florianwns/keyboard-fatar-tp40/images/IMG_2003.jpg

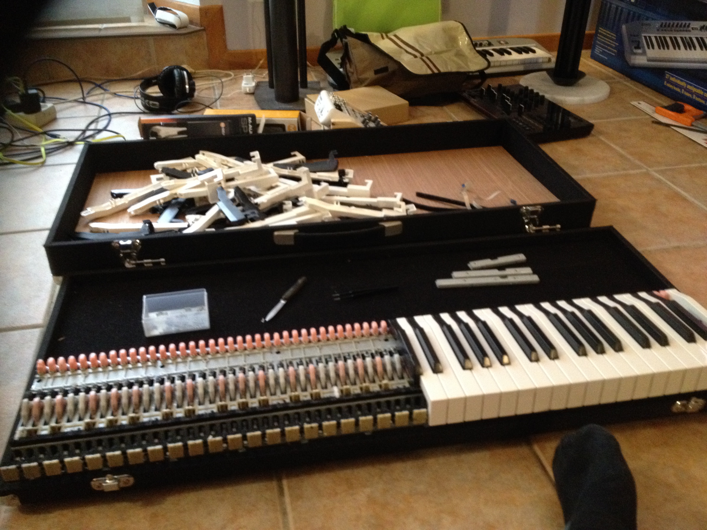
images/IMG_2003.jpg
