florianwns/keyboard-fatar-tp40/images/IMG_2004.jpg

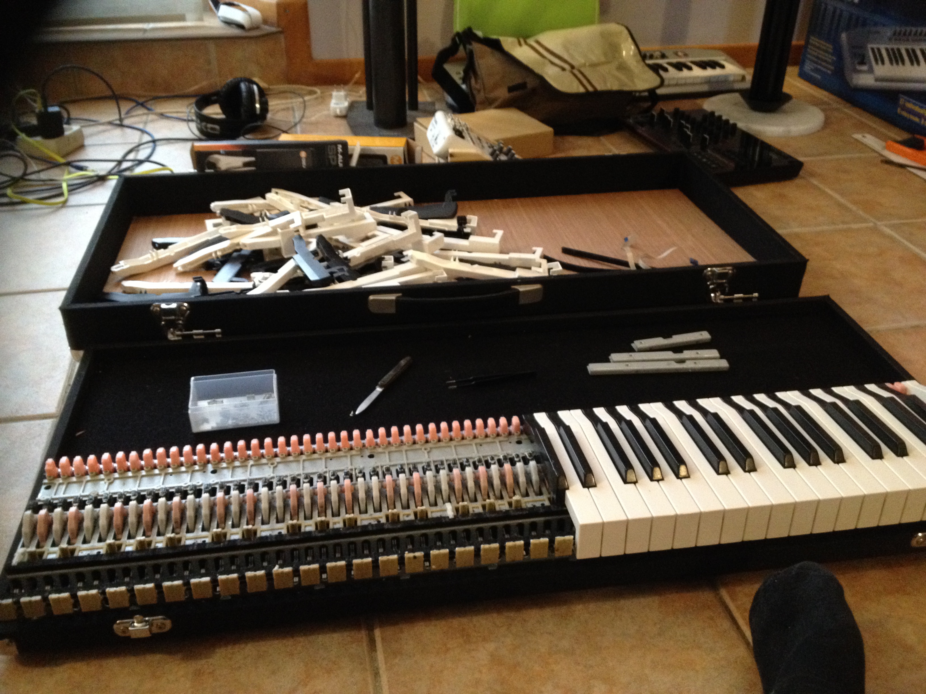
images/IMG_2004.jpg
