florianwns/keyboard-fatar-tp40/images/IMG_2005.jpg

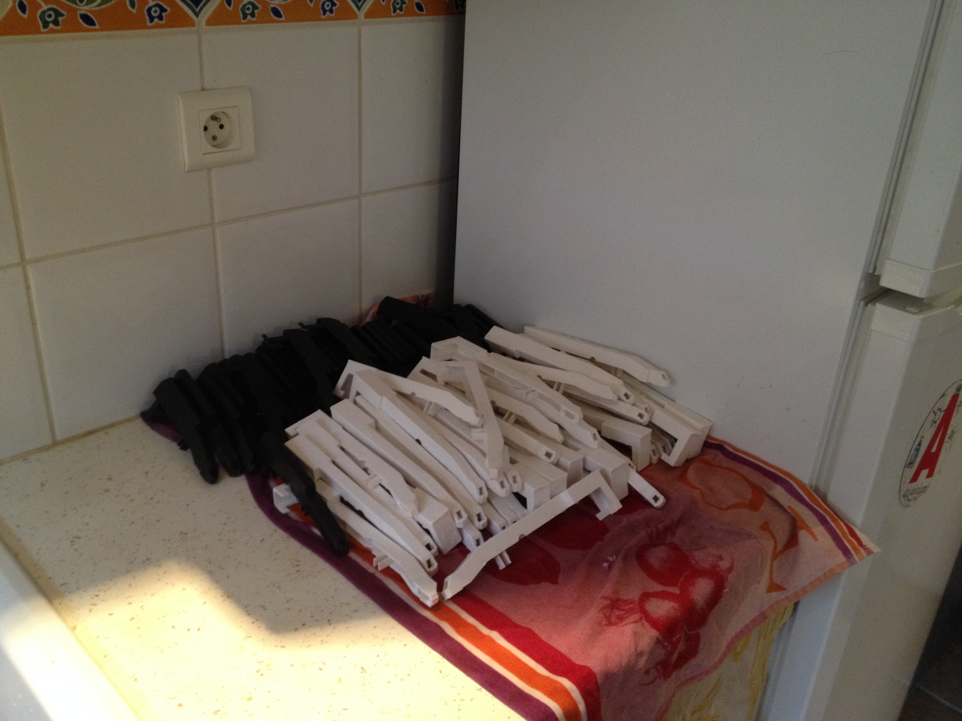
images/IMG_2005.jpg
