florianwns/keyboard-fatar-tp40/images/IMG_2006.jpg

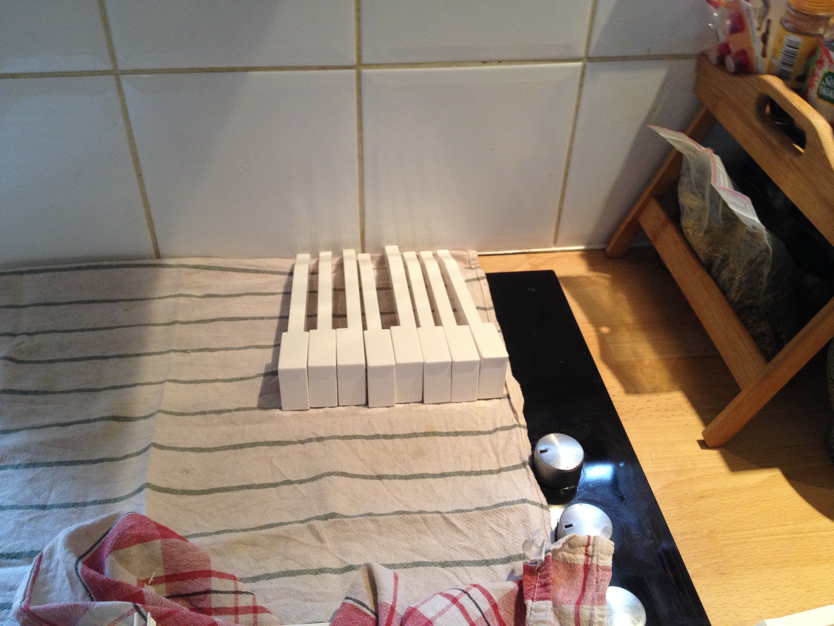
images/IMG_2006.jpg
