florianwns/keyboard-fatar-tp40/images/IMG_2008.jpg

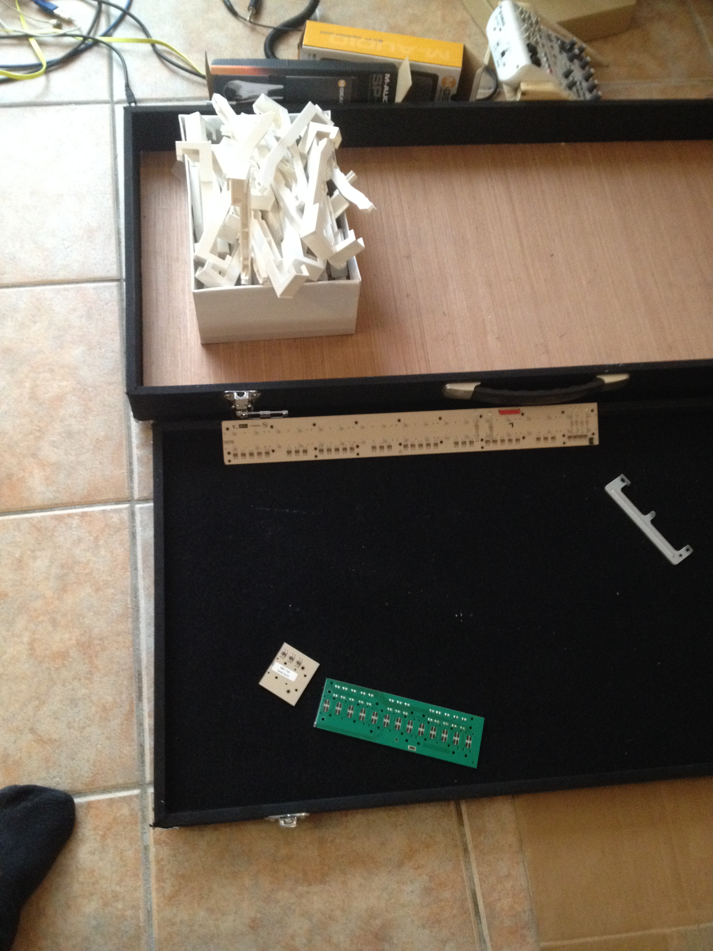
images/IMG_2008.jpg
