florianwns/keyboard-fatar-tp40/images/IMG_2009.jpg

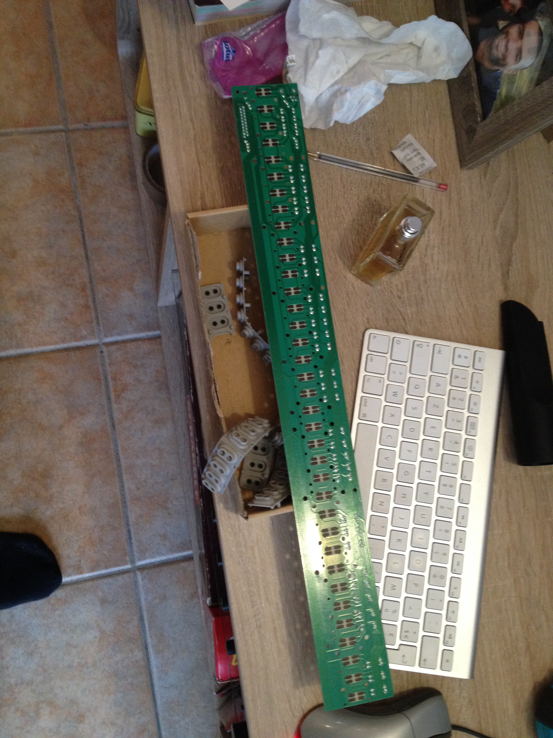
images/IMG_2009.jpg
