florianwns/keyboard-fatar-tp40/images/IMG_2011.jpg

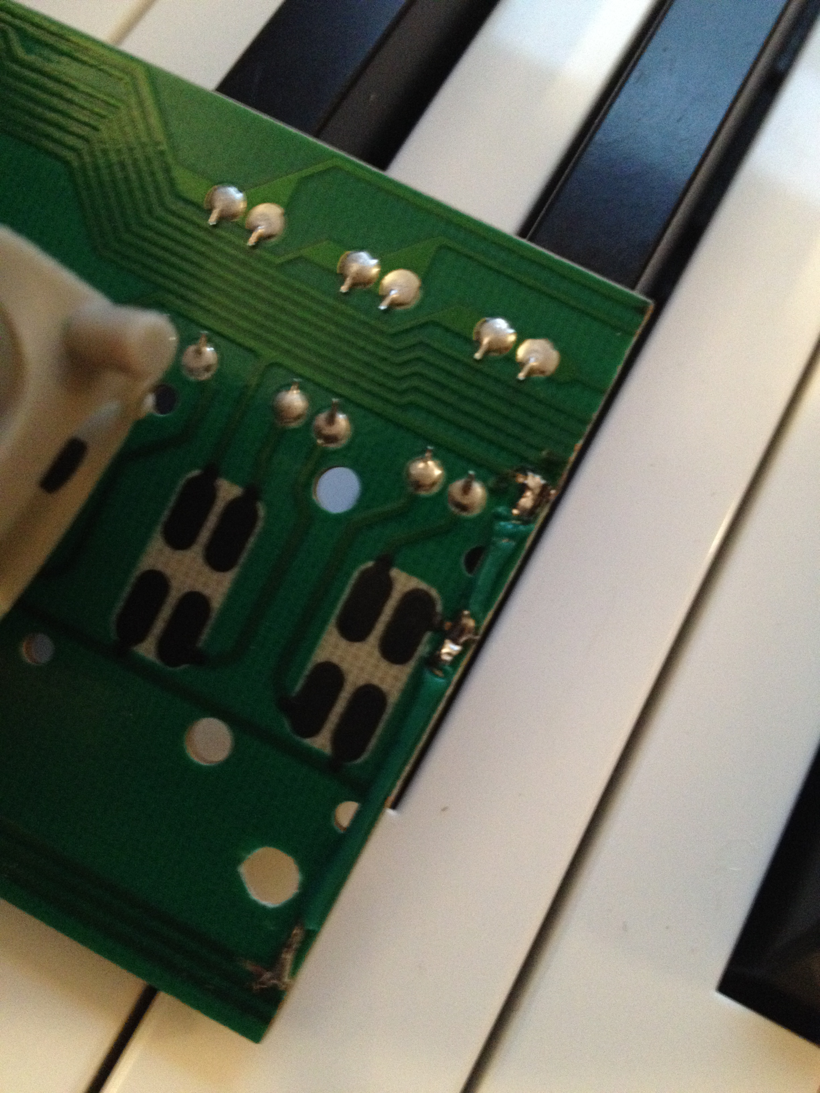
images/IMG_2011.jpg
