florianwns/keyboard-fatar-tp40/images/IMG_2012.jpg

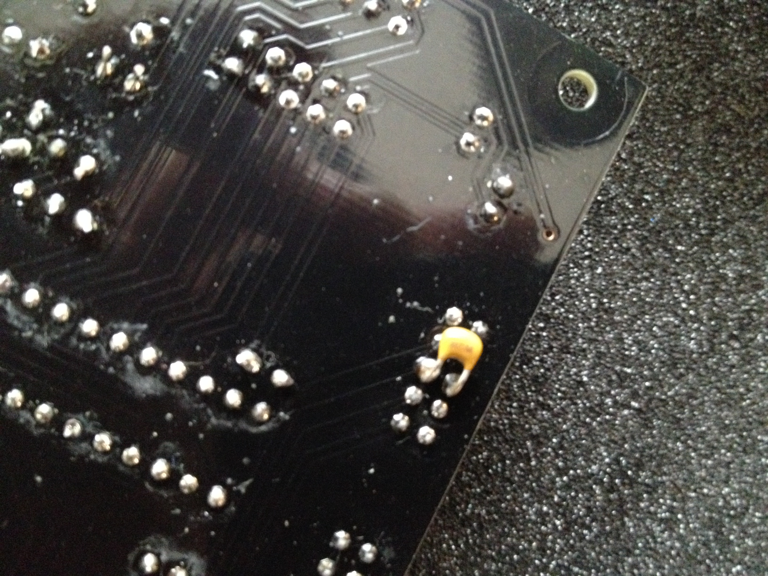
images/IMG_2012.jpg
