florianwns/keyboard-fatar-tp40/images/IMG_2013.jpg

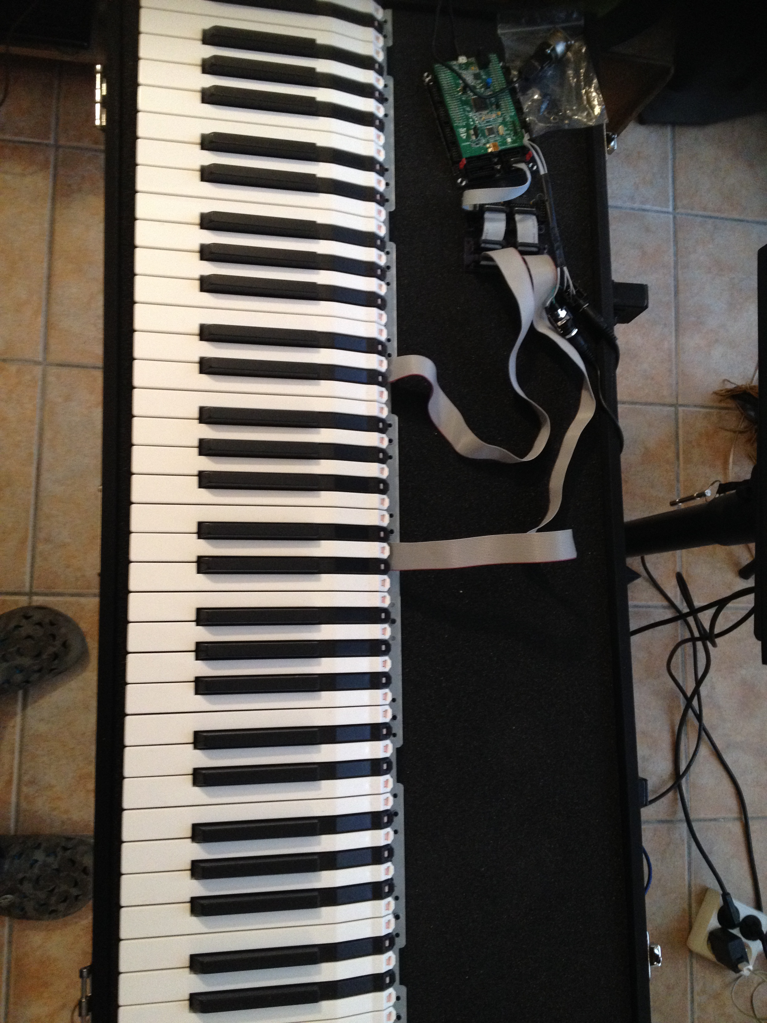
images/IMG_2013.jpg
