florianwns/keyboard-fatar-tp40/images/IMG_2017.jpg

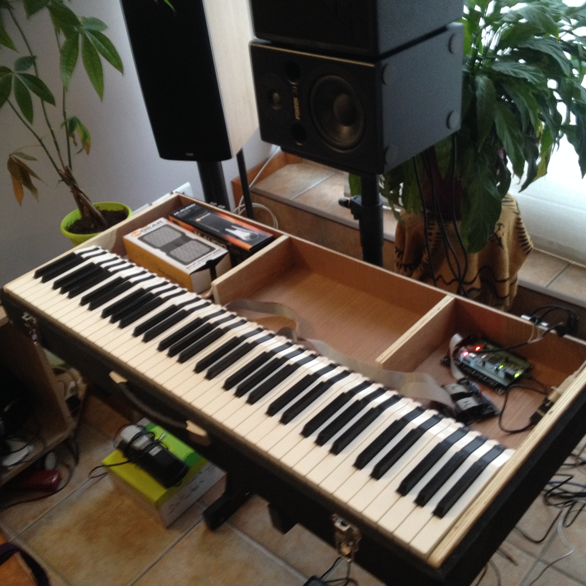
images/IMG_2017.jpg
