florianwns/keyboard-fatar-tp40/images/IMG_2021.jpg

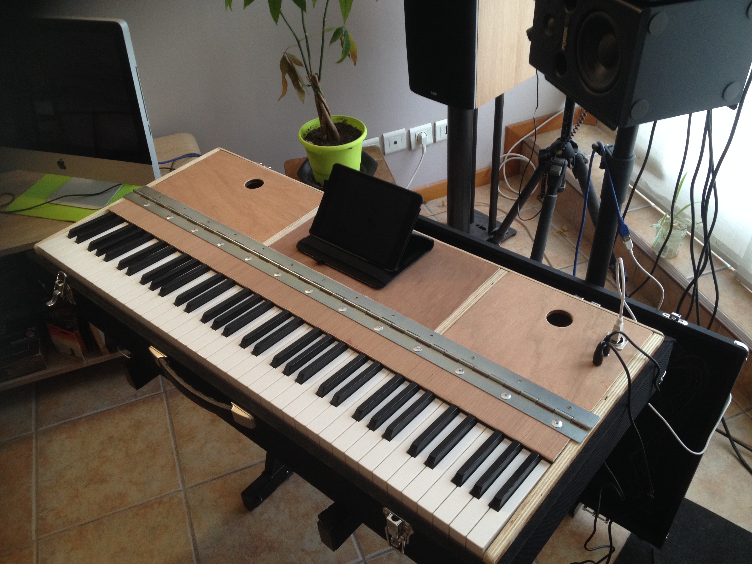
images/IMG_2021.jpg
