florianwns/keyboard-fatar-tp40/stm32f4/Matrix_76.gif

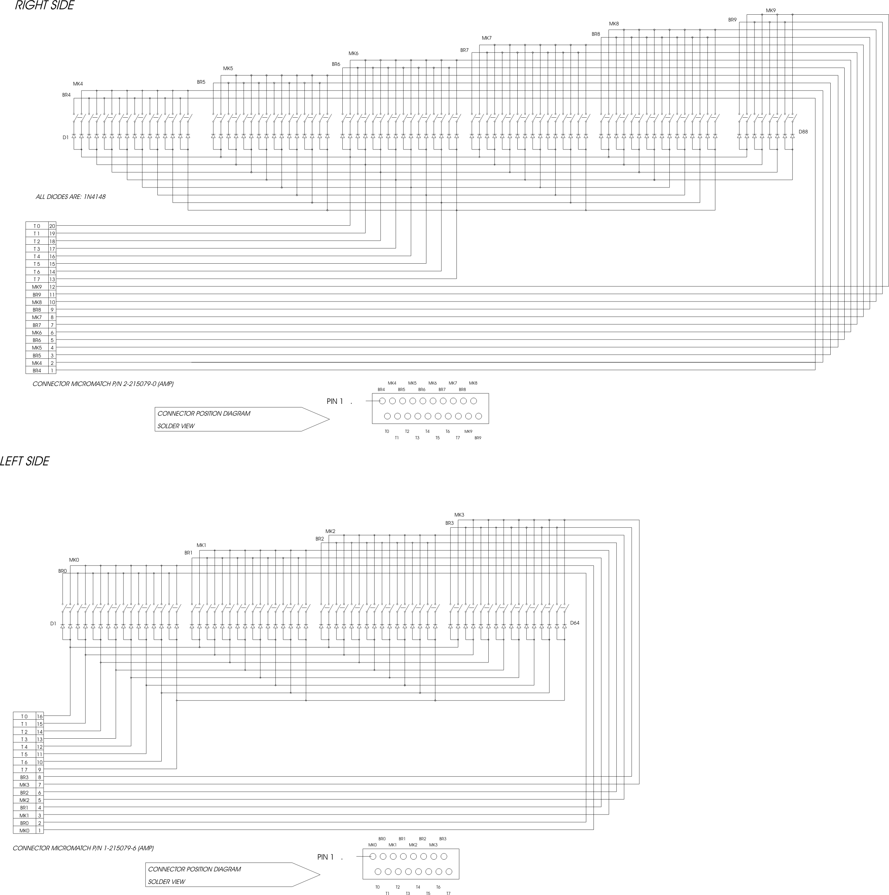
stm32f4/Matrix_76.gif
