florianwns/keyboard-fatar-tp40/stm32f4/mbhp_core_stm32f4_0.jpg

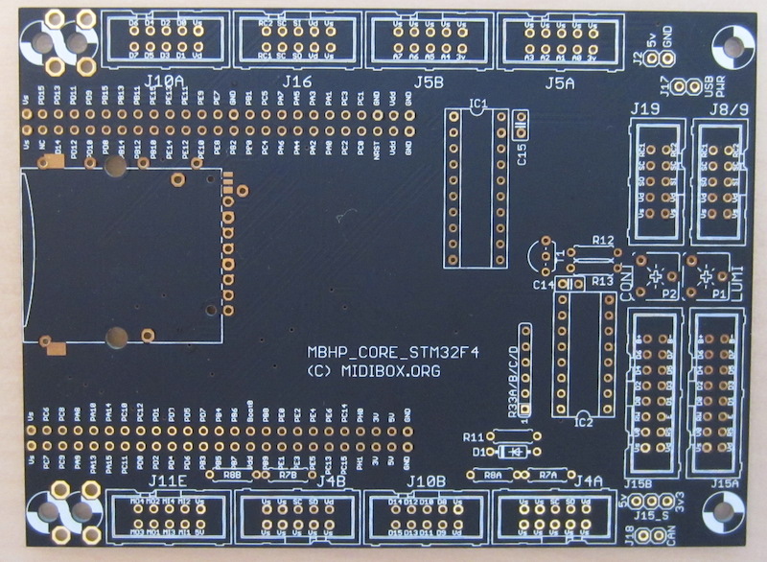
stm32f4/mbhp_core_stm32f4_0.jpg
