florianwns/keyboard-fatar-tp40/velocity/Velocity 1 - 127.logicx/Alternatives/000/WindowImage.jpg

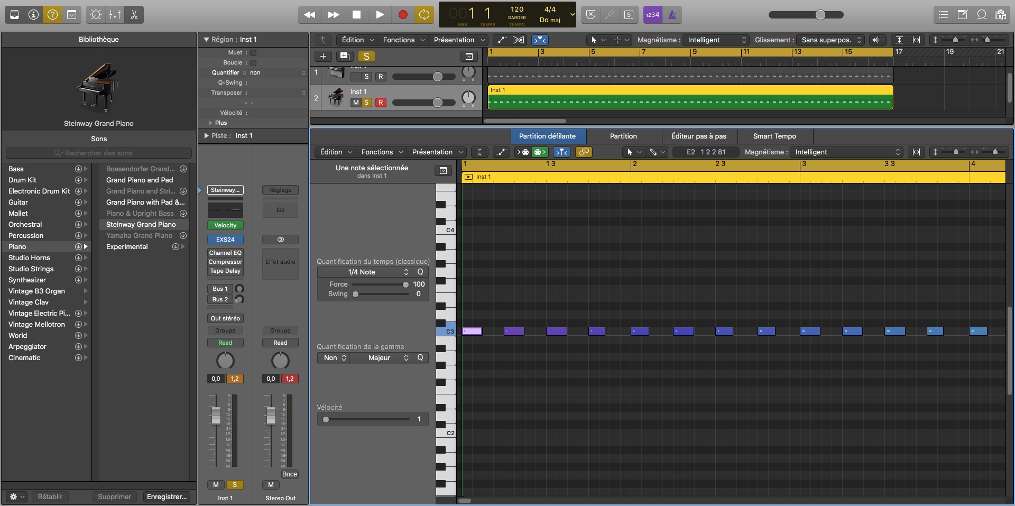
velocity/Velocity 1 - 127.logicx/Alternatives/000/WindowImage.jpg
