florianwns/keyboard-fatar-tp40/installation/3 - select MIDI IN & OUT.png

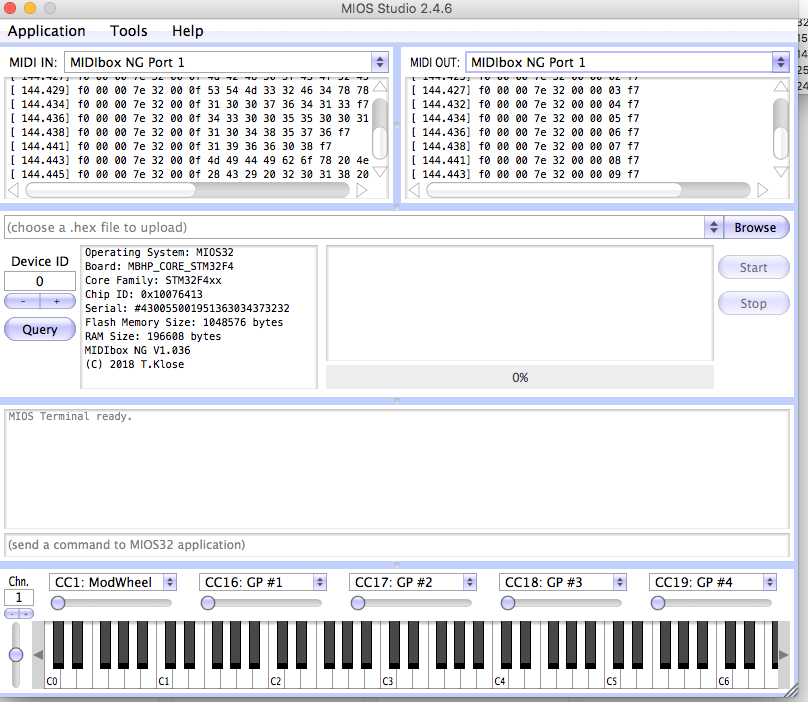
installation/3 - select MIDI IN & OUT.png
